kkr0kk/c172-xpndr/SolidWorks files/chassis_adaptateur.SLDPRT

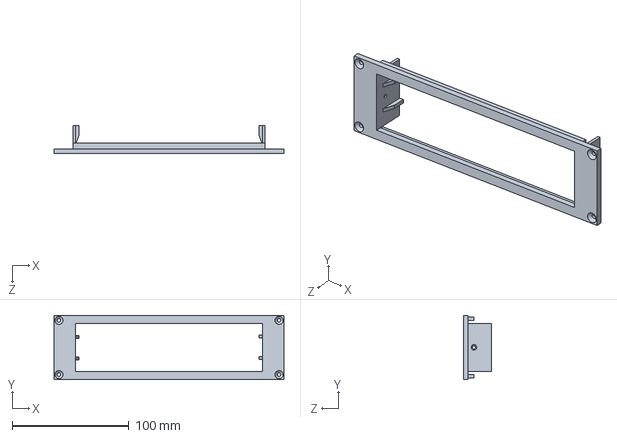
[picture p23: CAD file, 2021-01-12]
SolidWorks files/chassis_adaptateur.SLDPRT
197.0 x 55.0 x 24.0 mm
